hanshuebner/mockingboard2k/kicad-libs/models/SOP-24_15.0x5.3mm_P1.27mm.scad

// cribbed from http://www.sl-alex.com.ua/en/page/3d-models-for-kicad-part1-openscad

use <case.scad>
use <pin.scad>

// Case dimensions
case_x=15;        // Case X dimension
case_y=5.3;        // Case Y dimension
case_z=1.85;        // Case Z dimension
case_a = 75;

notch_d=0.6;
notch_depth=0.1;
notch_x=0.8;
notch_y=0.8;

// Pin arrays parameters
side1_pins = 12;
side2_pins = 0;
side3_pins = 12;
side4_pins = 0;
pin_distance =1.27;    // Pin step

// Pin parameters
pin_th = 0.2; // Thickness
pin_W = 0.45;  // Pin width
pin_L = 1.3;  // Total Length
pin_H = case_z/2+pin_th/2; // Pin height (from bottom to top)
pin_l = 0.5;  // Length of the bottom part
pin_a = 115;  // Bending angle


// Array of pins
// _cnt - number of pins
// _distance - distance between pin centres
module pins_array(_cnt, _distance)
{
	if (_cnt>0)
	{
		for (_i = [0:_cnt-1])
		{
			translate([_distance*_i,0,0])
				pin(pin_L,pin_l,pin_H,pin_th,pin_a,pin_W);
		}
	}
}

// Complete model
union()
{
	// Top pins
	translate([(side1_pins-side3_pins)*pin_distance/2,case_y+pin_L*2,0])
		mirror([0,1,0])
			pins_array(side3_pins, pin_distance);

	// Bottom pins
	pins_array(side1_pins, pin_distance);

	// Left pins
	translate([-(case_x-(side1_pins-1)*pin_distance)/2 - pin_L,pin_L+case_y/2-(side4_pins-1)*pin_distance/2,0])
		mirror([1,0,0])
			rotate([0,0,90])
				pins_array(side4_pins, pin_distance);

	// Right pins
	translate([-(case_x-(side1_pins-1)*pin_distance)/2-pin_L+case_x+2*pin_L,pin_L+case_y/2-(side2_pins-1)*pin_distance/2,0])
		mirror([0,1,0])
			mirror([0,1,0])
				rotate([0,0,90])
					pins_array(side2_pins, pin_distance);

	// Case
	translate([-(case_x-(side1_pins-1)*pin_distance)/2,pin_L,0])
		case(case_x,case_y,case_z,pin_H,pin_th,case_a,case_a,case_a,case_a,case_a,case_a,case_a,case_a, notch_x,notch_y,notch_d,notch_depth);
}
